pseudoincorrect/Wootch/Embedded_firmware/Wootch/support/image_assets/resized_150x150/sleepy_dog.jpg

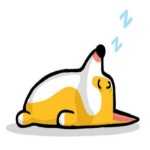
Embedded_firmware/Wootch/support/image_assets/resized_150x150/sleepy_dog.jpg
